mikhailmishurinskikh/Namotchik/CAD/rail/Square Rail Linear Ball Bearing - 2816093/images/IMG_7985.JPG

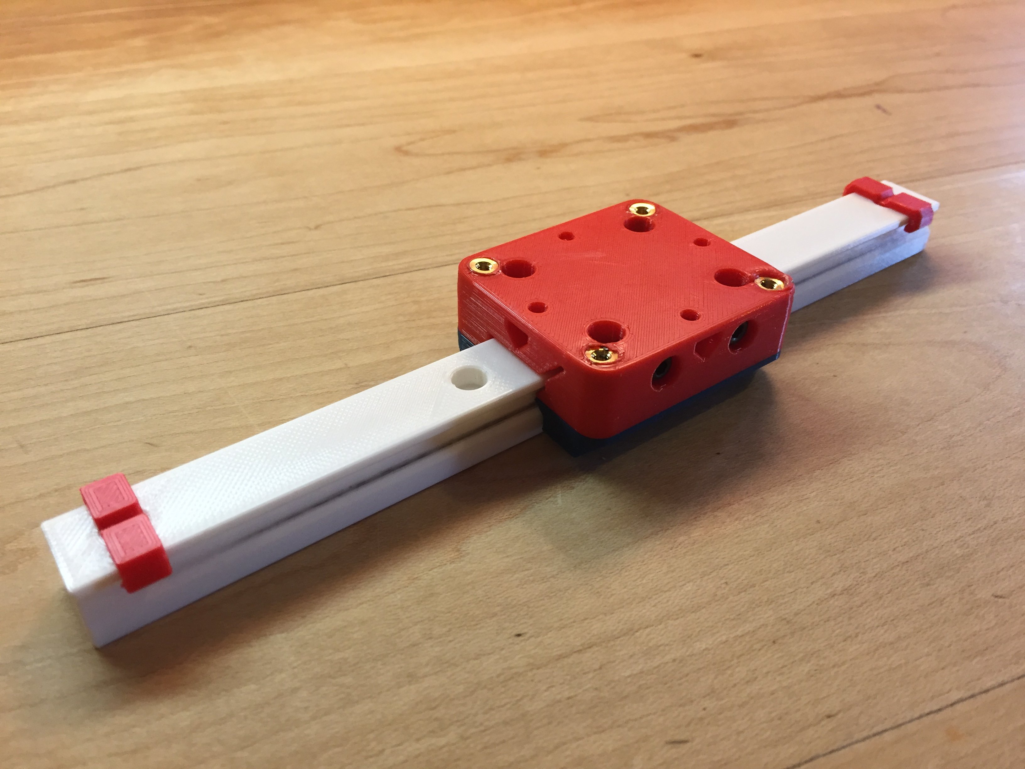
CAD/rail/Square Rail Linear Ball Bearing - 2816093/images/IMG_7985.JPG
