mikhailmishurinskikh/Namotchik/CAD/rail/Square Rail Linear Ball Bearing - 2816093/files/LB-V1-BEARING_COVER.stl

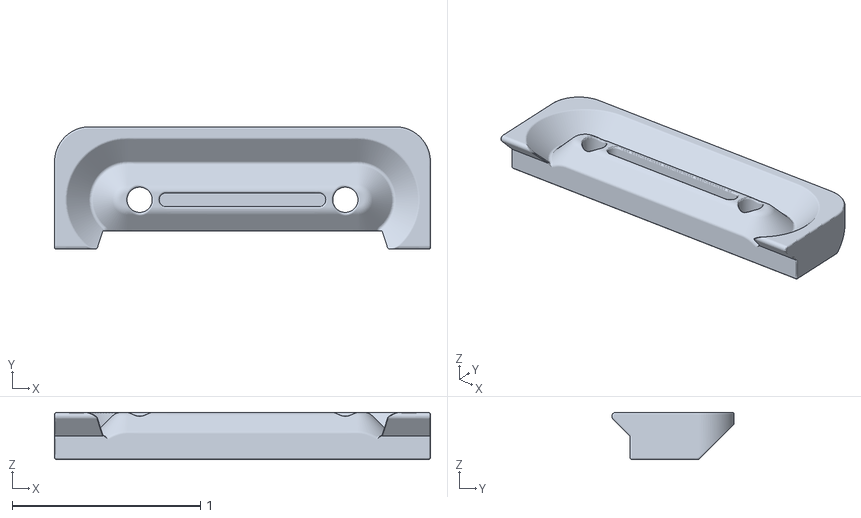
[picture p26: CAD file, 2025-05-15]
CAD/rail/Square Rail Linear Ball Bearing - 2816093/files/LB-V1-BEARING_COVER.stl
2.00 x 0.652 x 0.25
