mikhailmishurinskikh/Namotchik/CAD/nemasmall/nema-17-pancake-17hs4023-1.snapshot.6/625ZZ.stp

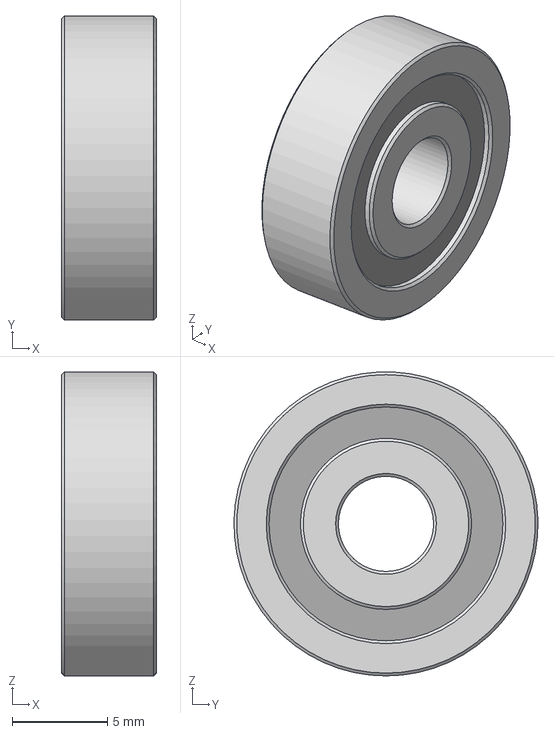
[picture p27: CAD file, 2025-05-15]
CAD/nemasmall/nema-17-pancake-17hs4023-1.snapshot.6/625ZZ.stp
5.00 x 16.0 x 16.0 mm
