mikhailmishurinskikh/Namotchik/CAD/plateUp.STEP

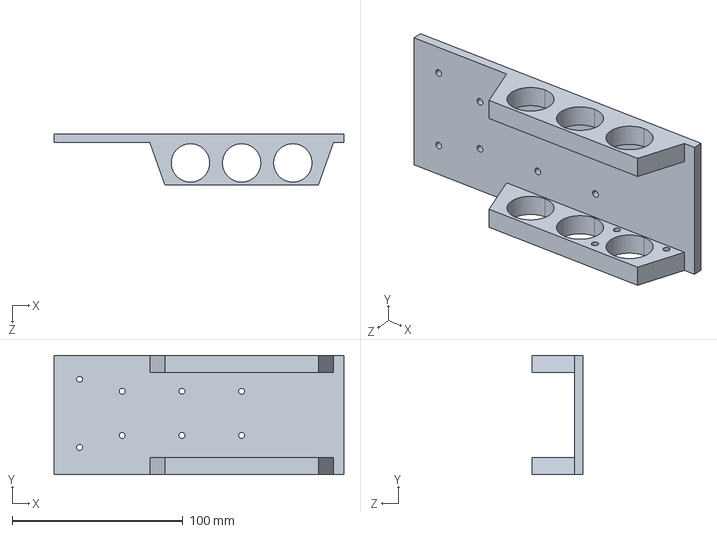
[picture p28: CAD file, 2025-05-15]
CAD/plateUp.STEP
170.0 x 70.0 x 30.0 mm
