mikhailmishurinskikh/Namotchik/CAD/holder.STEP

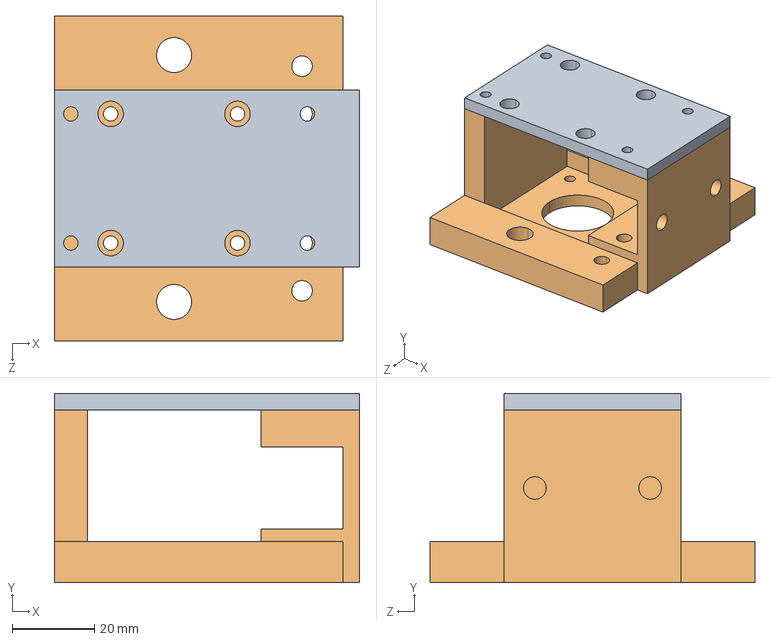
[picture p29: CAD file, 2025-05-15]
CAD/holder.STEP
74.2 x 46.0 x 79.0 mm
