mikhailmishurinskikh/Namotchik/CAD/nemasmall/nema-17-pancake-17hs4023-1.snapshot.6/back_plate.stp

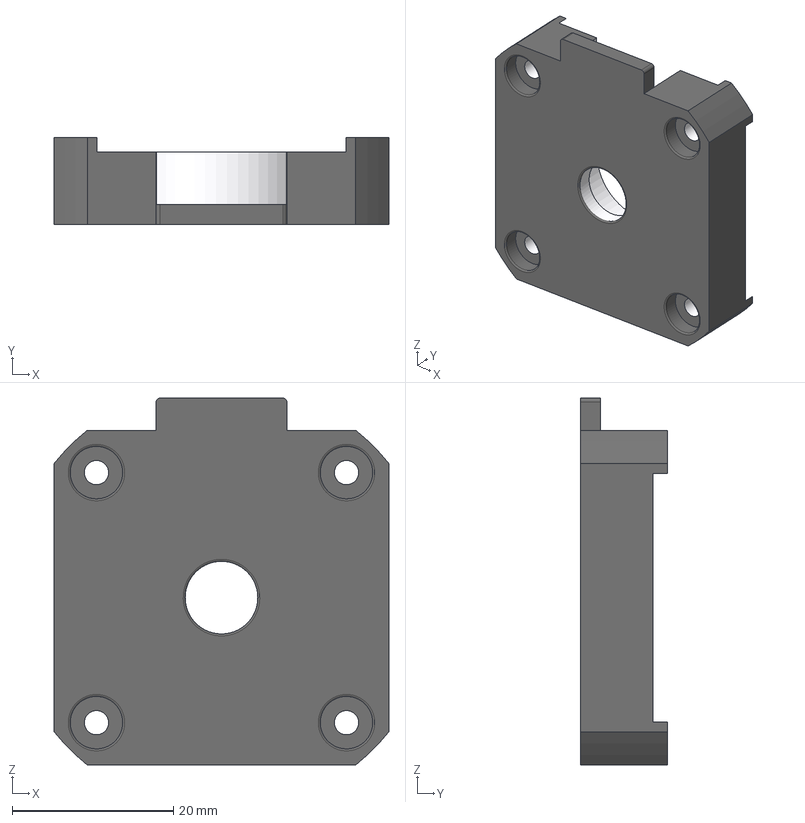
[picture p30: CAD file, 2025-05-15]
CAD/nemasmall/nema-17-pancake-17hs4023-1.snapshot.6/back_plate.stp
41.5 x 10.8 x 45.5 mm
