mikhailmishurinskikh/Namotchik/CAD/shkiv.SLDPRT

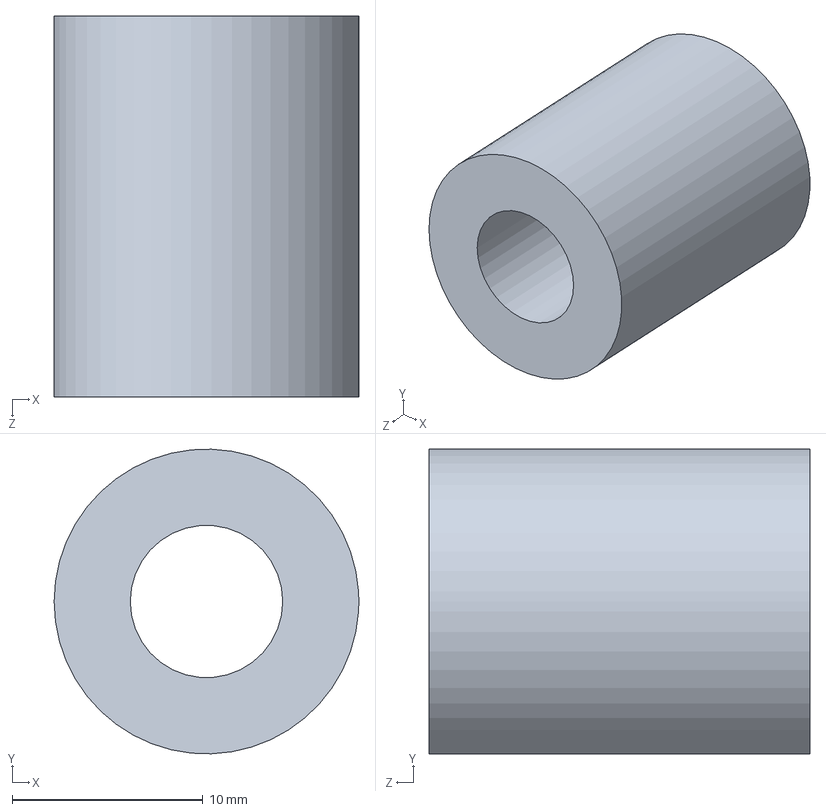
[picture p31: CAD file, 2025-05-15]
CAD/shkiv.SLDPRT
16.0 x 16.0 x 20.0 mm
