mikhailmishurinskikh/Namotchik/CAD/Move_holder.STEP

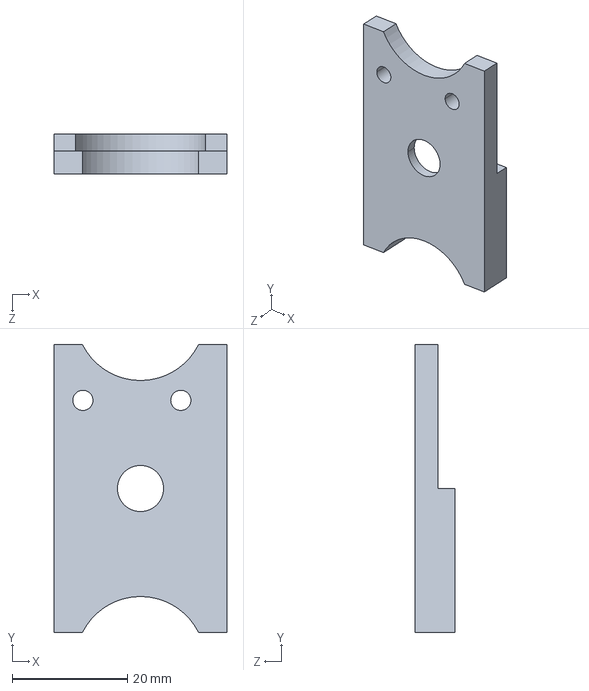
[picture p32: CAD file, 2025-05-15]
CAD/Move_holder.STEP
30.0 x 50.0 x 7.00 mm
