mikhailmishurinskikh/Namotchik/CAD/nemasmall/nema-17-pancake-17hs4023-1.snapshot.6/front_plate.stp

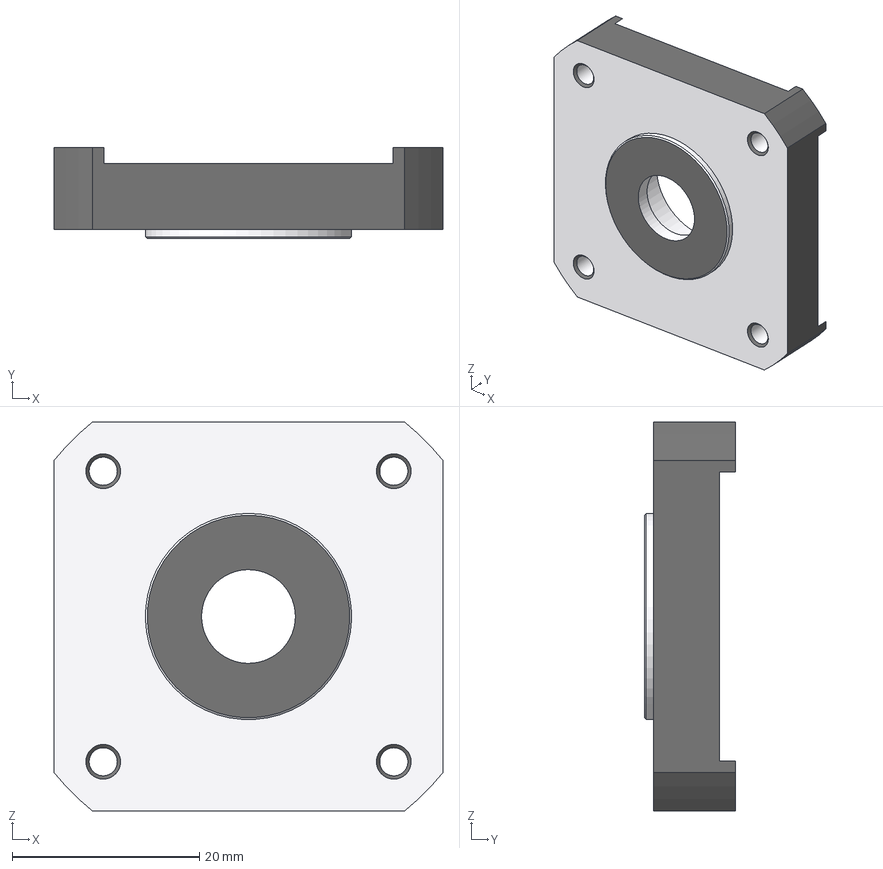
[picture p33: CAD file, 2025-05-15]
CAD/nemasmall/nema-17-pancake-17hs4023-1.snapshot.6/front_plate.stp
41.5 x 9.75 x 41.5 mm
