mikhailmishurinskikh/Namotchik/CAD/plate.STEP

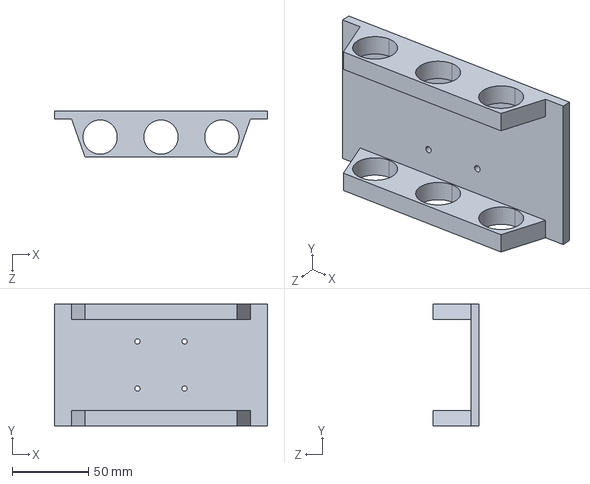
[picture p34: CAD file, 2025-05-15]
CAD/plate.STEP
140.0 x 80.0 x 30.0 mm
