mikhailmishurinskikh/Namotchik/CAD/holder-2.SLDPRT

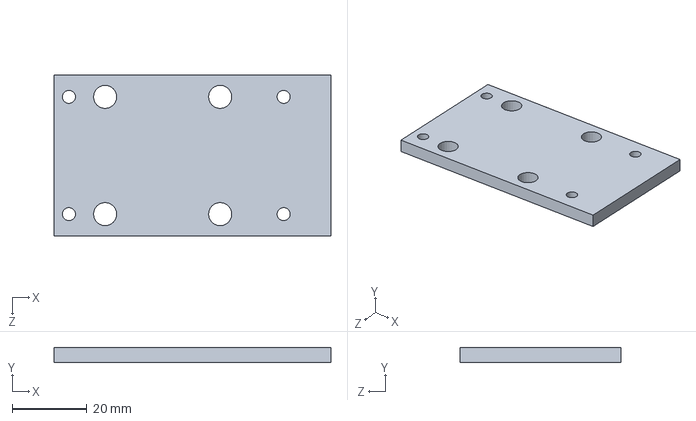
[picture p35: CAD file, 2025-05-15]
CAD/holder-2.SLDPRT
74.2 x 4.00 x 43.0 mm
