mikhailmishurinskikh/Namotchik/CAD/star.STEP

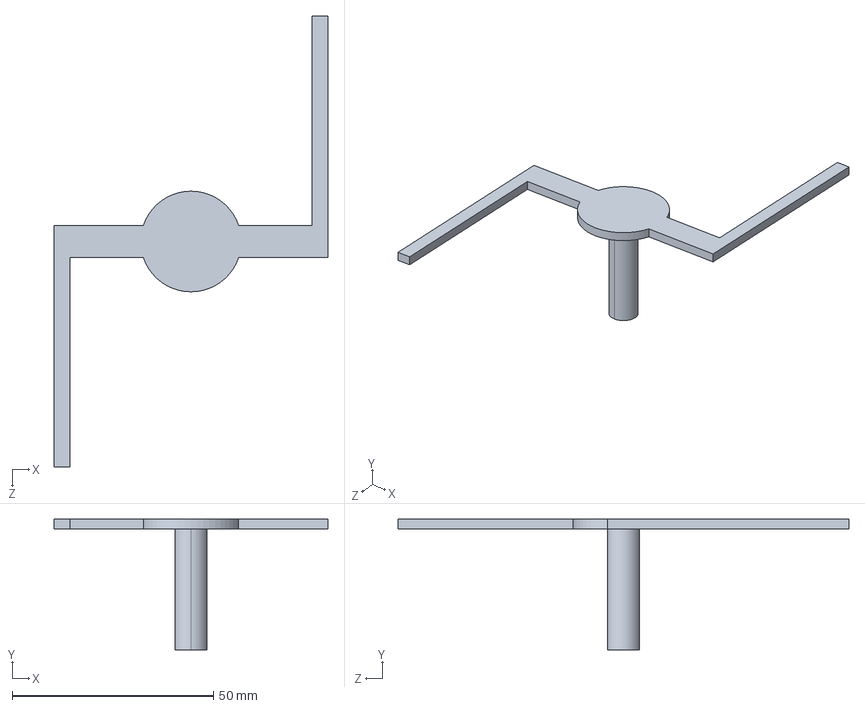
[picture p36: CAD file, 2025-05-15]
CAD/star.STEP
68.0 x 32.5 x 112.0 mm
