mikhailmishurinskikh/Namotchik/CAD/fixskiv.STEP

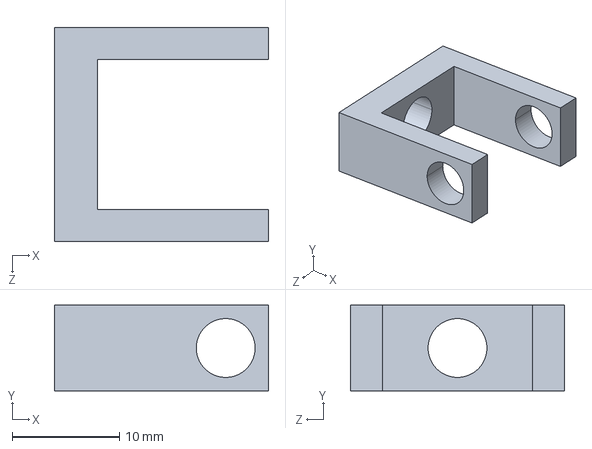
[picture p37: CAD file, 2025-05-15]
CAD/fixskiv.STEP
20.0 x 8.00 x 20.0 mm
