mikhailmishurinskikh/Namotchik/CAD/DownShort.SLDPRT

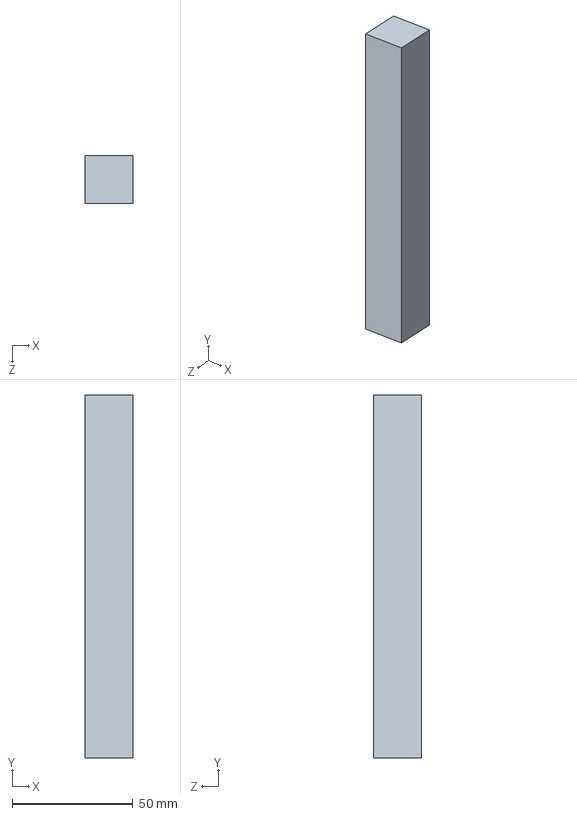
[picture p38: CAD file, 2025-05-15]
CAD/DownShort.SLDPRT
20.0 x 150.0 x 20.0 mm
