mikhailmishurinskikh/Namotchik/CAD/UpLong.SLDPRT

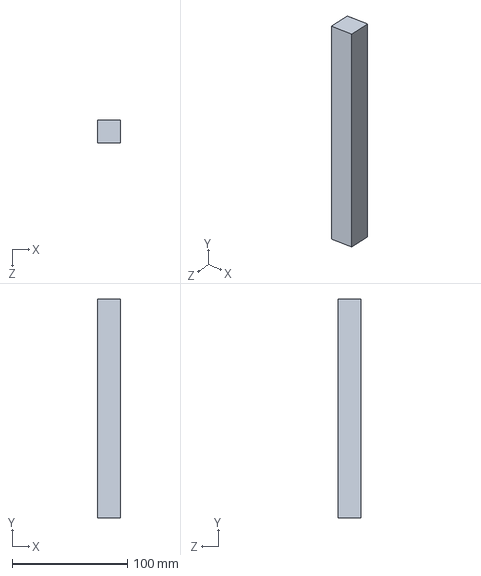
[picture p39: CAD file, 2025-05-15]
CAD/UpLong.SLDPRT
20.0 x 190.0 x 20.0 mm
