mikhailmishurinskikh/Namotchik/CAD/threeUp.STEP

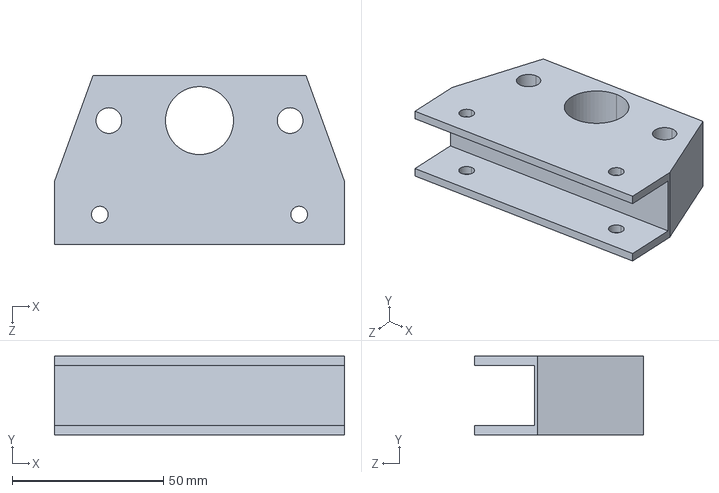
[picture p40: CAD file, 2025-05-15]
CAD/threeUp.STEP
96.0 x 26.0 x 56.1 mm
