mikhailmishurinskikh/Namotchik/CAD/beltbear.SLDPRT

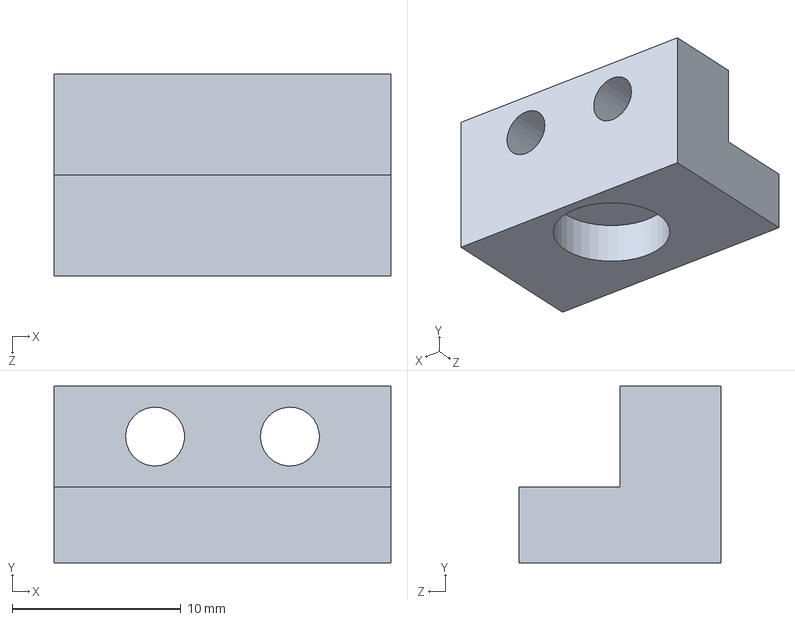
[picture p41: CAD file, 2025-05-15]
CAD/beltbear.SLDPRT
20.0 x 10.5 x 12.0 mm
