mikhailmishurinskikh/Namotchik/CAD/pipe.STEP

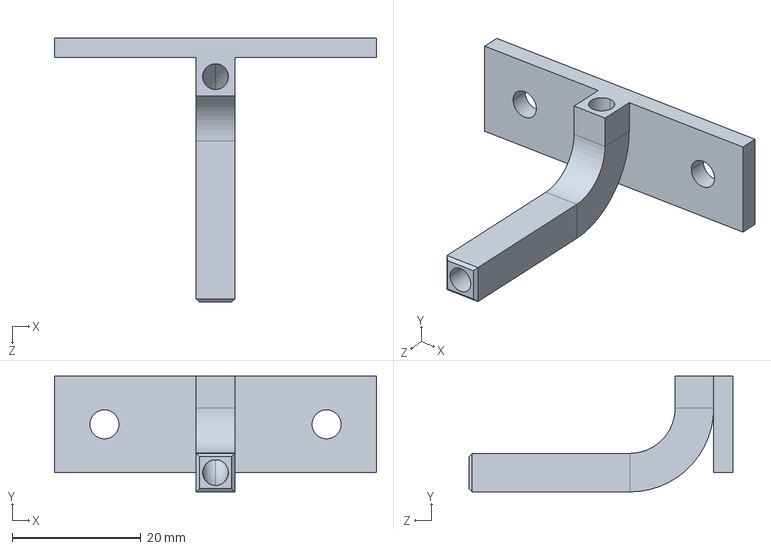
[picture p42: CAD file, 2025-05-15]
CAD/pipe.STEP
50.0 x 18.0 x 41.0 mm
