mikhailmishurinskikh/Namotchik/CAD/RailDown.SLDPRT

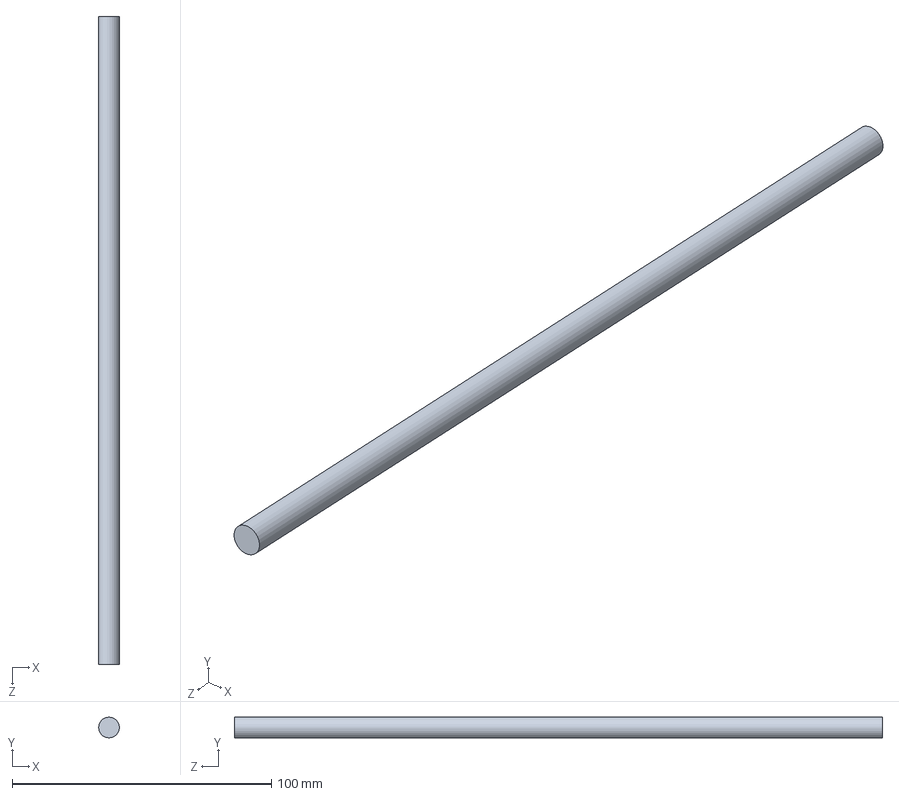
[picture p43: CAD file, 2025-05-15]
CAD/RailDown.SLDPRT
8.00 x 7.99 x 250.0 mm
