mikhailmishurinskikh/Namotchik/CAD/DownLong.SLDPRT

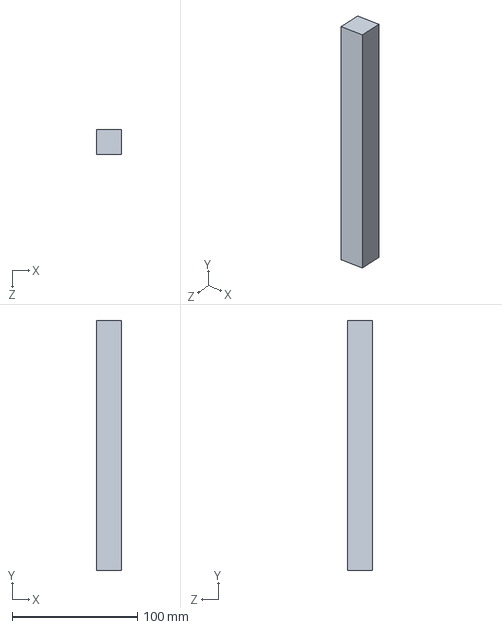
[picture p44: CAD file, 2025-05-15]
CAD/DownLong.SLDPRT
20.0 x 200.0 x 20.0 mm
