mikhailmishurinskikh/Namotchik/CAD/Bearing.SLDPRT

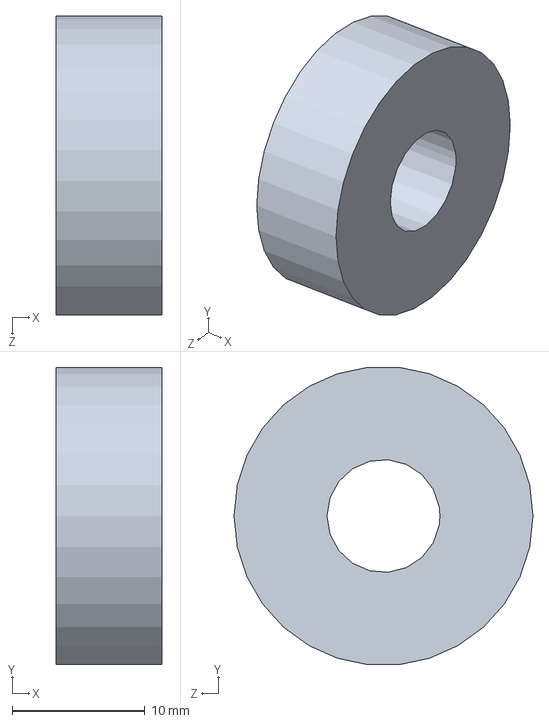
[picture p45: CAD file, 2025-05-15]
CAD/Bearing.SLDPRT
8.00 x 22.4 x 22.5 mm
