mikhailmishurinskikh/Namotchik/CAD/plastina.STEP

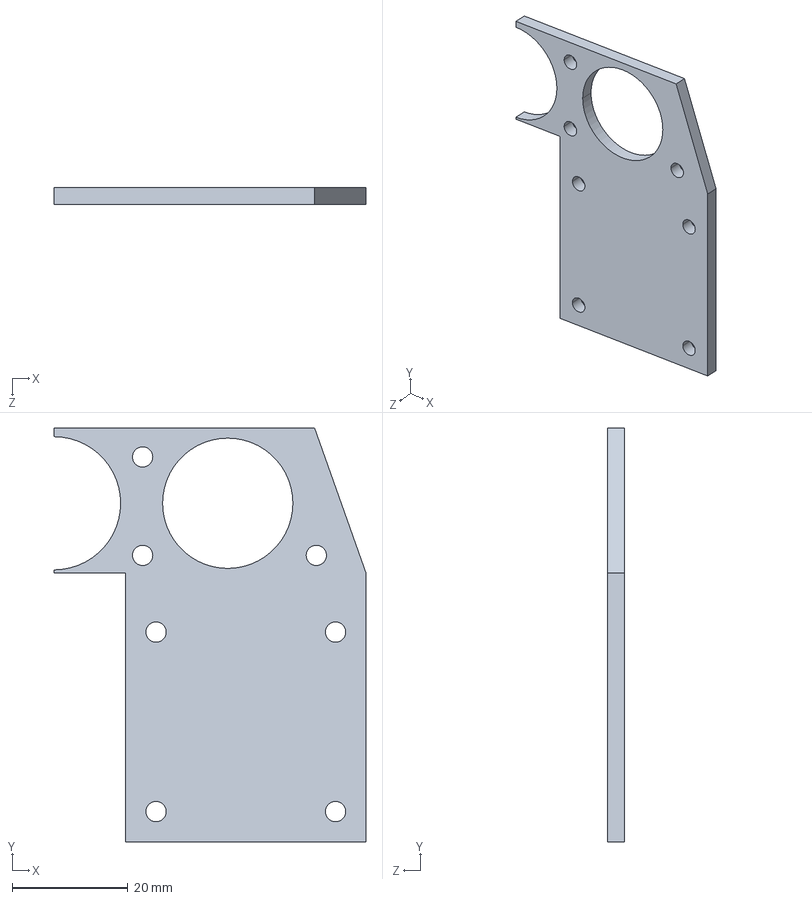
[picture p46: CAD file, 2025-05-15]
CAD/plastina.STEP
53.9 x 71.5 x 3.00 mm
