mikhailmishurinskikh/Namotchik/CAD/shkivNATYAZ.SLDPRT

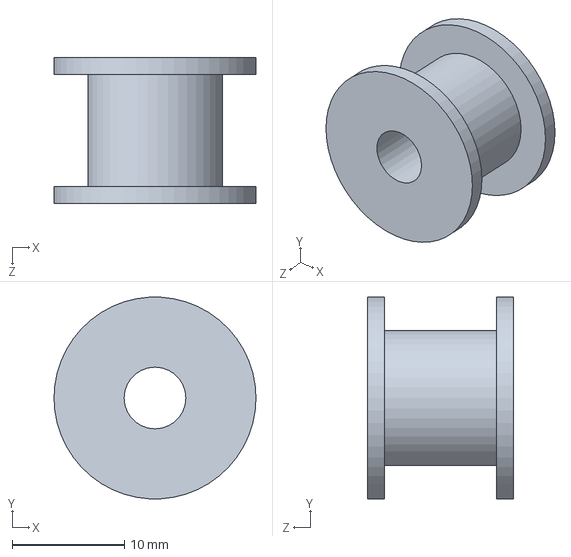
[picture p47: CAD file, 2025-05-15]
CAD/shkivNATYAZ.SLDPRT
18.0 x 18.0 x 13.0 mm
