mikhailmishurinskikh/Namotchik/CAD/new_holder.STEP

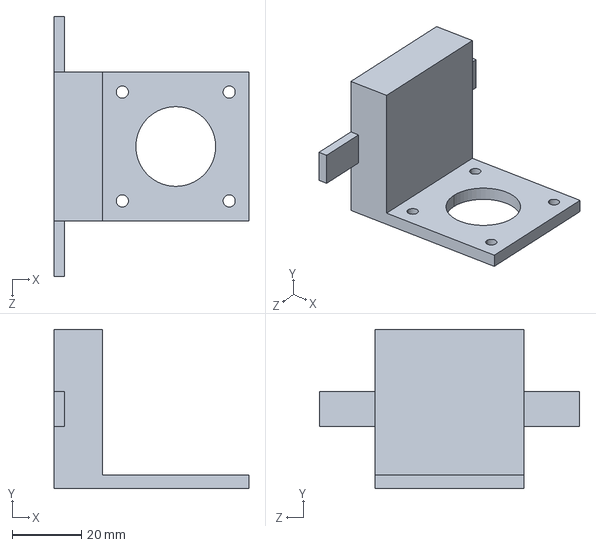
[picture p48: CAD file, 2025-05-15]
CAD/new_holder.STEP
56.2 x 46.0 x 75.0 mm
