mikhailmishurinskikh/Namotchik/CAD/railWORK.STEP

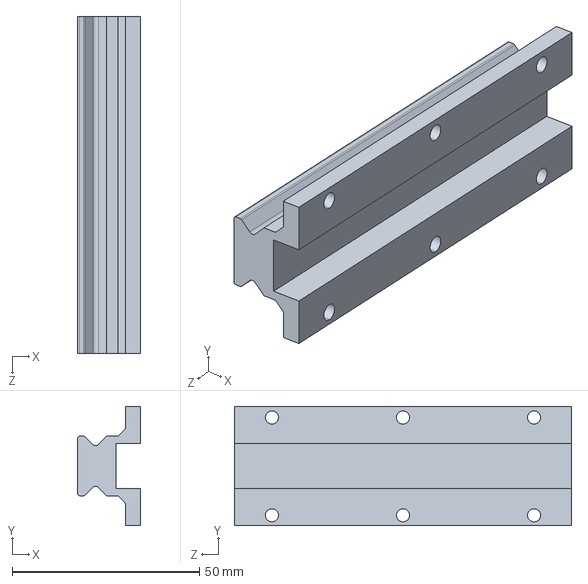
[picture p49: CAD file, 2025-05-15]
CAD/railWORK.STEP
16.7 x 31.9 x 90.0 mm
