mikhailmishurinskikh/Namotchik/CAD/load.SLDASM

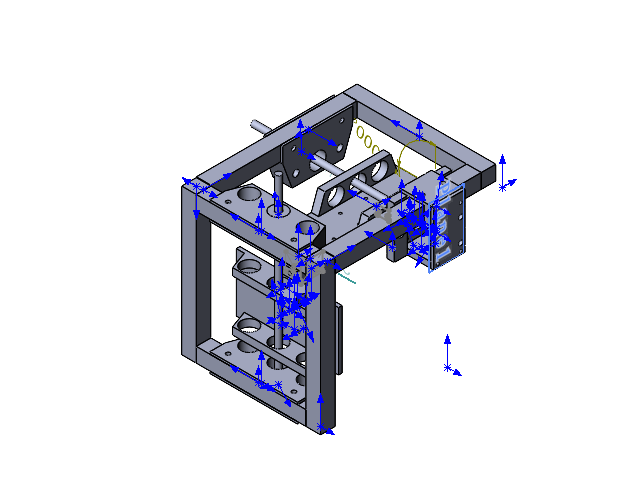
[picture p50: CAD file, 2025-05-15]
CAD/load.SLDASM
DownLong x 4
DownShort x 2
Bearing x 2
RailDown x 2
UpLong
three x 2
plate
holder
threeUp
plateUp
shkivNATYAZ
shkiv
back_plate.stp x 2
front_plate.stp x 2
stator.stp x 2
625ZZ.stp x 4
rotor.stp x 2
connector.stp x 2
M3_screw.stp x 8
fixskiv
fixfixskiv
plastina
railWORK
